sMsElectronics/Kawari-Power-Sequencer/Documentation/KPS_Interconnect.pdf

# (KPS) KAWARI POWER SEQUENCER INTERCONNECTION (SEE PAGE TWO

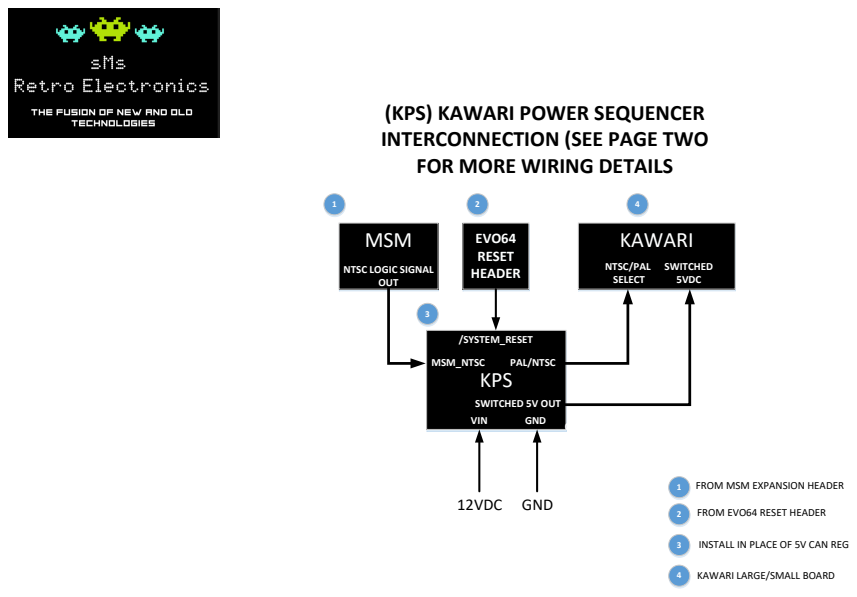
[picture p15: page 1]
MSM; EVO64; RESET HEADER; KAWARI; KPS; OUT; NTSC/PAL SELECT; 12VDC GND; SWITCHED 5VDC; /SYSTEM_RESET; SWITCHED 5V OUT; MSM_NTSC; PAL/NTSC; VIN; GND

FOR MORE WIRING DETAILS

NTSC LOGIC SIGNAL

1 FROM MSM EXPANSION HEADER

2 FROM EVO64 RESET HEADER

3 INSTALL IN PLACE OF 5V CAN REG

4 KAWARI LARGE/SMALL BOARD

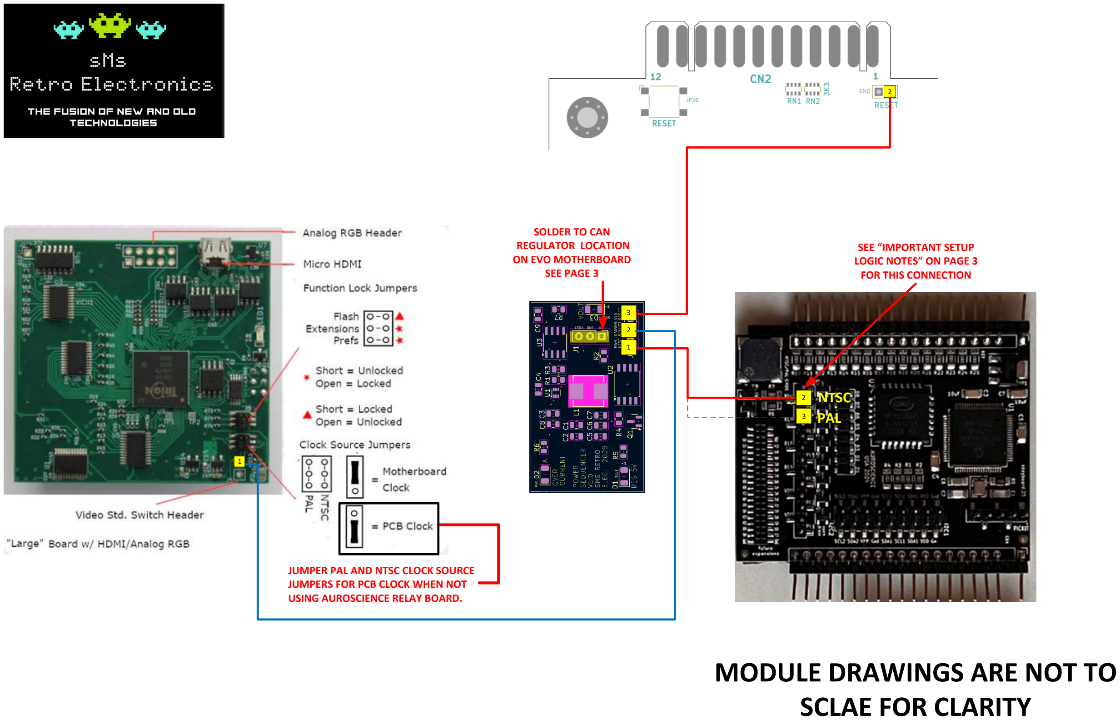
[picture p16: page 2]

JUMPER PAL AND NTSC CLOCK SOURCE JUMPERS FOR PCB CLOCK WHEN NOT USING AUROSCIENCE RELAY BOARD.

2

1

SOLDER TO CAN
REGULATOR LOCATION
ON EVO MOTHERBOARD
SEE PAGE 3

# MODULE DRAWINGS ARE NOT TO SCLAE FOR CLARITY

3

2

## NTSC

2

1

## 3 PAL

SEE “IMPORTANT SETUP
LOGIC NOTES” ON PAGE 3
FOR THIS CONNECTION

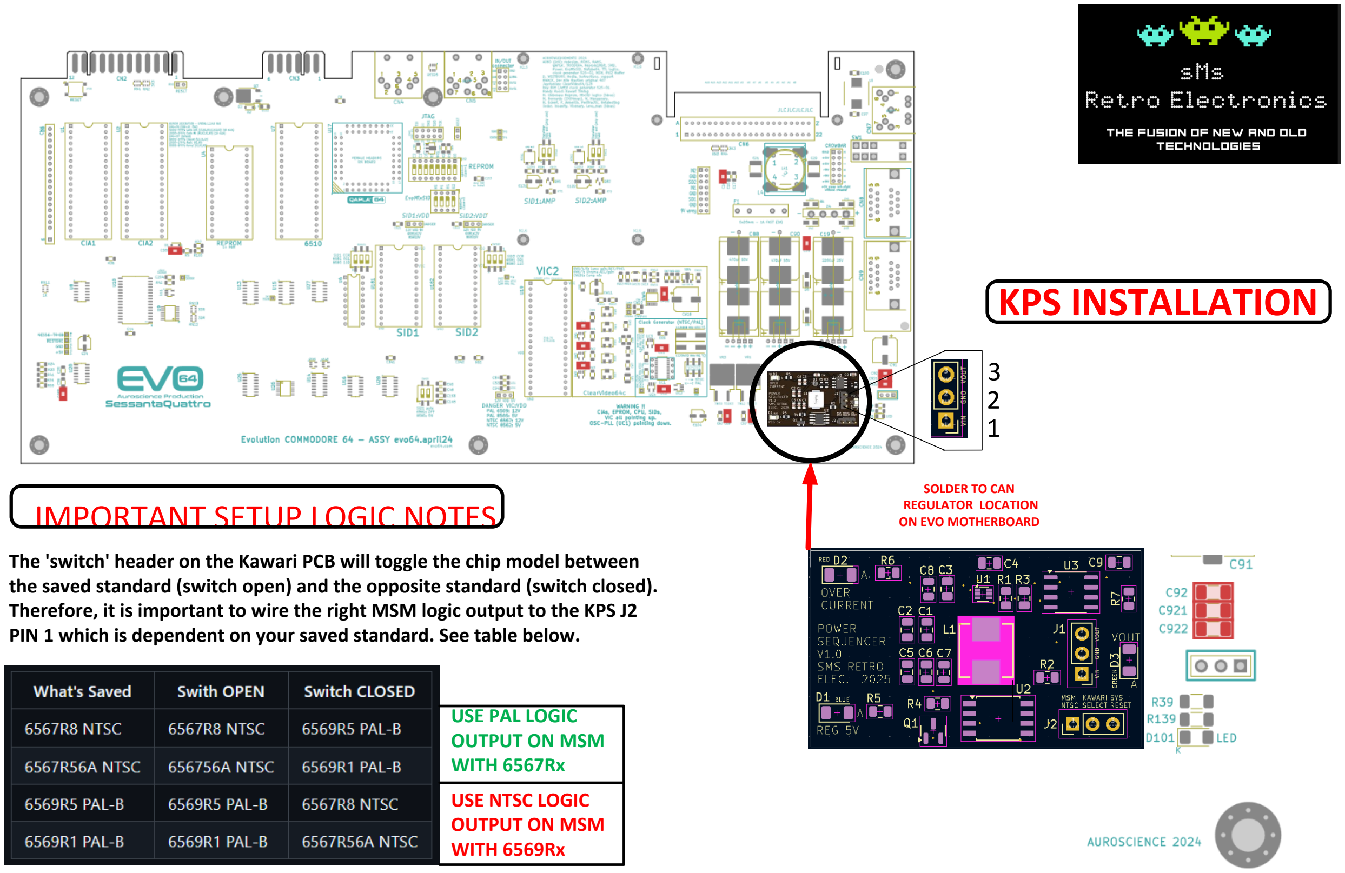
[picture p17: page 3]

SOLDER TO CAN
REGULATOR LOCATION
ON EVO MOTHERBOARD

1

2

3

## The 'switch' header on the Kawari PCB will toggle the chip model between

the saved standard (switch open) and the opposite standard (switch closed). Therefore, it is important to wire the right MSM logic output to the KPS J2

PIN 1 which is dependent on your saved standard. See table below.

## USE NTSC LOGIC OUTPUT ON MSM WITH 6569Rx

## USE PAL LOGIC OUTPUT ON MSM WITH 6567Rx

# IMPORTANT SETUP LOGIC NOTES

# KPS INSTALLATION
